colincreasman/zmk-sweep-v2/config/my_keymap.png

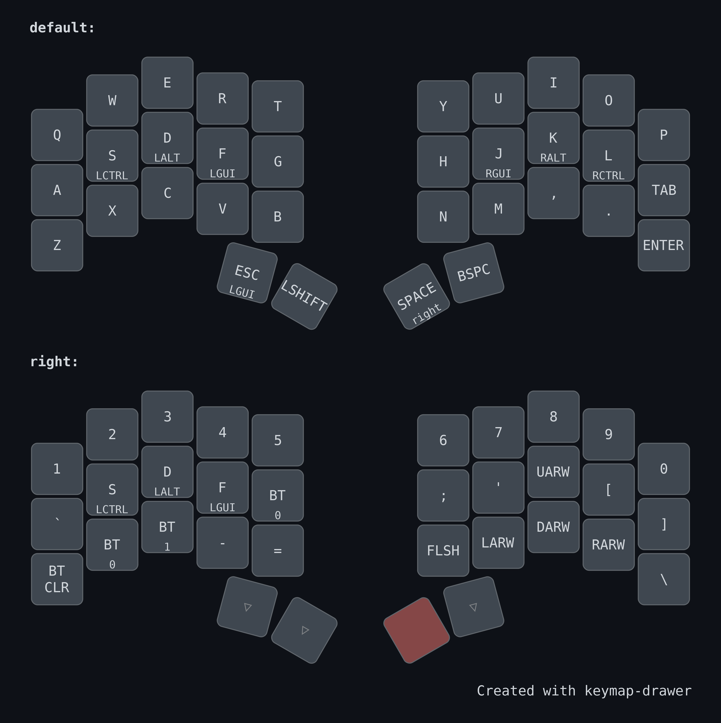
config/my_keymap.png
